swift502/MagChess/app/sensors.py

from random import randint

from constants import SENSOR_THRESHOLD_HIGH, SENSOR_THRESHOLD_LOW

class SensorProvider:
    def get_value_array(self) -> dict[tuple[int, int], float]:
        raise NotImplementedError()
    
class HWSensors(SensorProvider):
    def __init__(self):
        raise NotImplementedError()

    def get_value_array(self):
        raise NotImplementedError()

class SWSensorObject:
    signal_strength = 500
    noise = 100

    def __init__(self, state: int):
        self.state = state

    def get_value(self):
        if self.state == -1:
            return randint(SENSOR_THRESHOLD_LOW - self.signal_strength, SENSOR_THRESHOLD_LOW + self.noise)
        elif self.state == 1:
            return randint(SENSOR_THRESHOLD_HIGH - self.noise, SENSOR_THRESHOLD_HIGH + self.signal_strength)
        else:
            return randint(SENSOR_THRESHOLD_LOW - self.noise, SENSOR_THRESHOLD_HIGH + self.noise)

    def set_state(self, state):
        self.state = state

class SWSensors (SensorProvider):
    sensors: dict[tuple[int, int], SWSensorObject]

    def __init__(self):
        self.sensors = {}

        for co_letter in range(8):
            for co_number in range(8):
                state = 0
                if co_number == 0 or co_number == 1:
                    state = 1
                if co_number == 6 or co_number == 7:
                    state = -1
                self.sensors[(co_letter, co_number)] = SWSensorObject(state)

    def get_value_array(self):
        values: dict[tuple[int, int], float] = {}
        for key, sensor in self.sensors.items():
            values[key] = float(sensor.get_value())
        return values

    def cycle_sensor_state(self, co_letter: int, co_number: int):
        current_state = self.sensors[(co_letter, co_number)].state
        if current_state == -1:
            new_state = 0
        elif current_state == 1:
            new_state = -1
        else:
            new_state = 1
        self.sensors[(co_letter, co_number)].set_state(new_state)
