swift502/MagChess/app/ui.py

import flet as ft
import asyncio
from pathlib import Path
import concurrent.futures

from data import DataLib

class MagChessUI:

    page: ft.Page
    root: ft.Control
    content_host: ft.Container
    overlay: ft.Stack
    replay_button: ft.ElevatedButton
    screens: list[ft.Control]
    _hide_task: concurrent.futures.Future

    # Colors
    # Green
    col_light = "#eeeed5"
    col_dark = "#7d945d"

    # Brown
    # col_light = "#f0d9b5"
    # col_dark = "#b58863"

    def __init__(self, page: ft.Page, debug: bool):
        self.page = page

        # tabs
        tab1 = self.tab_1()
        tab2 = self.tab_2()
        tab3 = self.tab_3()
        self.screens = [tab1, tab2, tab3]

        if debug:
            self.root = ft.Row(
                controls=[
                    ft.Container(content=self.screens[0], width=720, height=720),
                    ft.Container(content=self.screens[1], width=720, height=720),
                    ft.Container(content=self.screens[2], width=720, height=720),
                ],
                spacing=0,
            )
            return

        # content host
        self.content_host = ft.Container(content=self.screens[1])

        self.overlay = self.get_overlay()

        self.root = ft.GestureDetector(
            on_hover=self.user_activity,
            hover_interval=150,
            on_tap=self.user_activity,
            on_pan_update=self.user_activity,
            content=ft.Stack(controls=[self.content_host, self.overlay]),
            height=720,
            width=720,
        )

    def tab_1(self):
        img = ft.Image(
            src= str(Path(__file__).parent / "assets/icons/correct.svg"),
            width=360,
            height=360,
        )

        text = ft.Text(
            "Correct",
            size=72,
            text_align=ft.TextAlign.CENTER,
            font_family="Noto Sans",
            color=ft.Colors.WHITE,
        )

        foreground = ft.Container(
            content=ft.Column(
                controls=[img, text],
                alignment=ft.MainAxisAlignment.CENTER,   # vertical centering
                horizontal_alignment=ft.CrossAxisAlignment.CENTER,  # horizontal centering
            ),
            alignment=ft.alignment.center,  # centers the whole Column in parent
            bgcolor=ft.Colors.with_opacity(0.8, "#96bc4b"),
        )

        return ft.Container(
            content=foreground,
            bgcolor=ft.Colors.BLACK,
        )

    def tab_2(self):

        stack: list = self.board(self.col_light, self.col_dark)

        pieces = {
            "a1": DataLib.pieces.white_rook,
            "b1": DataLib.pieces.white_knight,
            "c1": DataLib.pieces.white_bishop,
            "d1": DataLib.pieces.white_queen,
            "e1": DataLib.pieces.white_king,
            "f1": DataLib.pieces.white_bishop,
            "g1": DataLib.pieces.white_knight,
            "h1": DataLib.pieces.white_rook,
            "a2": DataLib.pieces.white_pawn,
            "b2": DataLib.pieces.white_pawn,
            "c2": DataLib.pieces.white_pawn,
            "d2": DataLib.pieces.white_pawn,
            "e2": DataLib.pieces.white_pawn,
            "f2": DataLib.pieces.white_pawn,
            "g2": DataLib.pieces.white_pawn,
            "h2": DataLib.pieces.white_pawn,
            "a8": DataLib.pieces.black_rook,
            "b8": DataLib.pieces.black_knight,
            "c8": DataLib.pieces.black_bishop,
            "d8": DataLib.pieces.black_queen,
            "e8": DataLib.pieces.black_king,
            "f8": DataLib.pieces.black_bishop,
            "g8": DataLib.pieces.black_knight,
            "h8": DataLib.pieces.black_rook,
            "a7": DataLib.pieces.black_pawn,
            "b7": DataLib.pieces.black_pawn,
            "c7": DataLib.pieces.black_pawn,
            "d7": DataLib.pieces.black_pawn,
            "e7": DataLib.pieces.black_pawn,
            "f7": DataLib.pieces.black_pawn,
            "g7": DataLib.pieces.black_pawn,
            "h7": DataLib.pieces.black_pawn,
        }

        for pos, piece in pieces.items():
            row = ord(pos[0]) - ord('a')
            col = int(pos[1]) - 1
            stack.append(ft.Image(
                src=piece.get_path(),
                width=80,
                height=80,
                left=col * 90 + 5,
                top=row * 90 + 5,
            ))

        return ft.Stack(
            controls=stack,
        )

    def tab_3(self):

        light = "#cccccc"
        dark = "#aaaaaa"

        sensor_positive = "#0000ff"
        sensor_negative = "#ff0000"
        sensor_neutral = "#000000"

        stack: list = self.board(light, dark)

        for i in range(8):
            for j in range(8):
                stack.append(ft.Container(
                    bgcolor=(i + j) % 2 == 1 and sensor_positive or sensor_negative,
                    width=20,
                    height=20,
                    border_radius=10,
                    left=j * 90 + 35,
                    top=i * 90 + 35,
                ))

        return ft.Stack(
            controls=stack,
        )
    
    def get_overlay(self):
        nav = ft.Container(
            content=ft.NavigationBar(
                selected_index=1,
                on_change=self.on_tab_change,
                destinations=[
                    ft.NavigationBarDestination(icon=ft.Icons.FORK_RIGHT, label="Moves"),
                    ft.NavigationBarDestination(icon=ft.Icons.CROP_FREE, label="Board"),
                    ft.NavigationBarDestination(icon=ft.Icons.SENSORS, label="Sensors"),
                ],
            ),
            border_radius=ft.border_radius.all(20),
            margin=ft.margin.only(left=16, right=16, bottom=16),
            left=0,
            right=0,
            bottom=0,
            shadow=ft.BoxShadow(
                color=ft.Colors.with_opacity(0.4, ft.Colors.BLACK),
                blur_radius=8,
                offset=ft.Offset(0, 4),
            ),
        )

        self.replay_button = ft.ElevatedButton(
            text=" " + "Review 5 moves",
            on_click=lambda e: print("Replay"),
            top=26,
            bgcolor="#6d10a3",
            color=ft.Colors.WHITE,
            icon=ft.Icons.HISTORY,
            style=ft.ButtonStyle(
                text_style=ft.TextStyle(size=30, font_family="Noto Sans"),
                icon_size=36,
                padding=ft.padding.symmetric(horizontal=34, vertical=26),
                shape=ft.ContinuousRectangleBorder(50),
            ),
        )

        return ft.Stack(
            controls=[nav, self.replay_button],
            animate_opacity=300,
            opacity=0.0,
            alignment=ft.alignment.center,
        )

    def board(self, light, dark):

        rows = []

        for r in range(8):
            row_cells = []
            for c in range(8):
                is_dark = (r + c) % 2 == 0
                cell = ft.Container(
                    expand=True,
                    bgcolor=dark if is_dark else light,
                )
                row_cells.append(cell)
            rows.append(
                ft.Row(
                    controls=row_cells,
                    spacing=0,
                    alignment=ft.MainAxisAlignment.CENTER,
                    aspect_ratio=8.0,
                )
            )

        board = ft.Column(
            controls=rows,
            spacing=0,
            aspect_ratio=1.0,
        )

        stack: list = [board]

        for i in range(8):
            stack.append(
                ft.Text(
                    str(i + 1),
                    size=30,
                    font_family="Noto Sans",
                    color= i % 2 == 1 and light or dark,
                    left= 90 * i + 66,
                    bottom= -3,
                )
            )

        for i in range(8):
            stack.append(
                ft.Text(
                    chr(ord('A') + i),
                    size=30,
                    font_family="Noto Sans",
                    color= i % 2 == 1 and dark or light,
                    left= 4,
                    top= 90 * i - 4,
                )
            )

        return stack

    def on_tab_change(self, e: ft.ControlEvent):
        idx = e.control.selected_index

        self.content_host.content = self.screens[idx]
        self.replay_button.visible = idx == 1
        
        self.page.update()
        self.user_activity()

    async def hide_after(self, seconds: float):
        try:
            # Wait
            await asyncio.sleep(seconds)

            # Hide
            self.overlay.opacity = 0.0
            self.page.update()
        except asyncio.CancelledError:
            pass

    def user_activity(self, _=None):
        # Show
        self.overlay.opacity = 1.0
        self.page.update()
        
        # Schedule hide
        if self._hide_task is not None:
            self._hide_task.cancel()
        self._hide_task = self.page.run_task(self.hide_after, 1.0)
